icegoat9/keychain_diceroller/docs/case_clamp.JPG

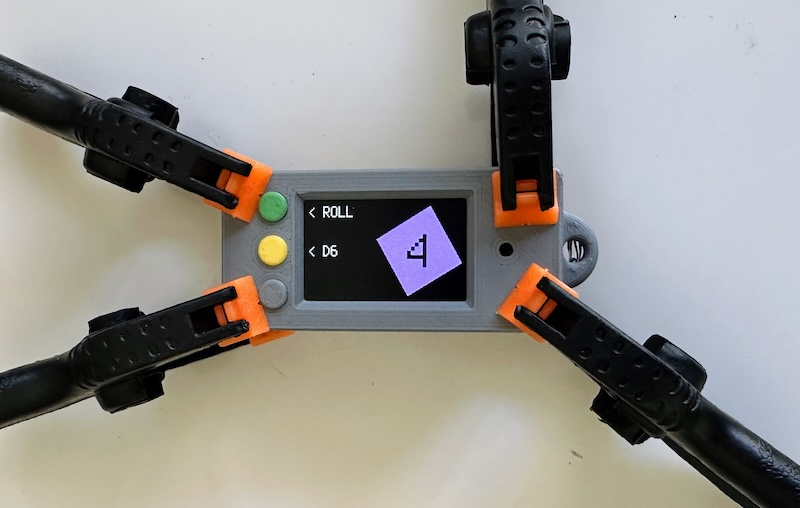
docs/case_clamp.JPG
