icegoat9/keychain_diceroller/docs/diceroll3.gif

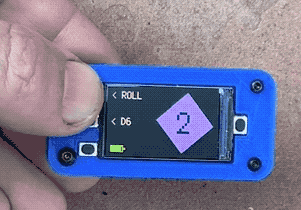
docs/diceroll3.gif
